pedroCollogno/DTYProject1/PCB/V0/V0 DTY MCAS_etch_silk_bottom.pdf

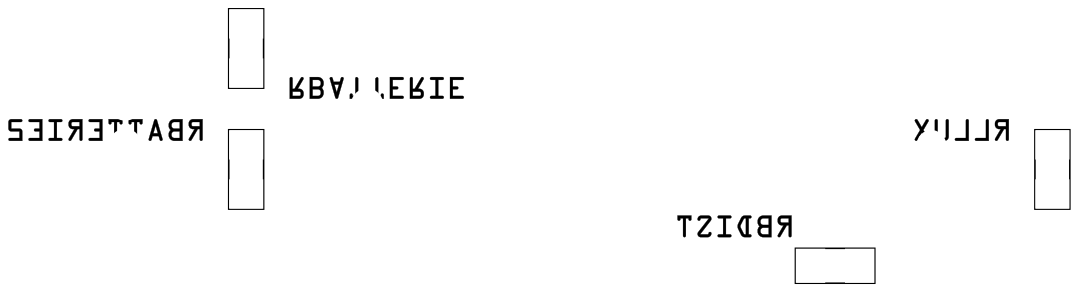
[picture p17: page 1]
