pedroCollogno/DTYProject1/PCB/V0/V0 DTY MCAS_etch_silk_bottom_mirror.pdf

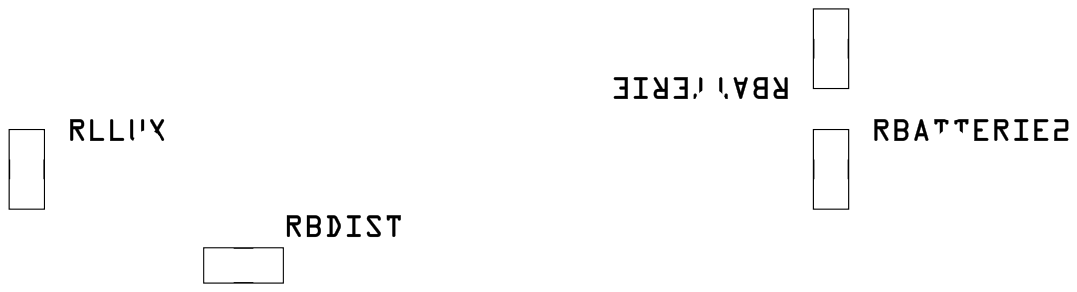
[picture p18: page 1]
