pedroCollogno/DTYProject1/PCB/V0/V0 DTY MCAS_etch_silk_top.pdf

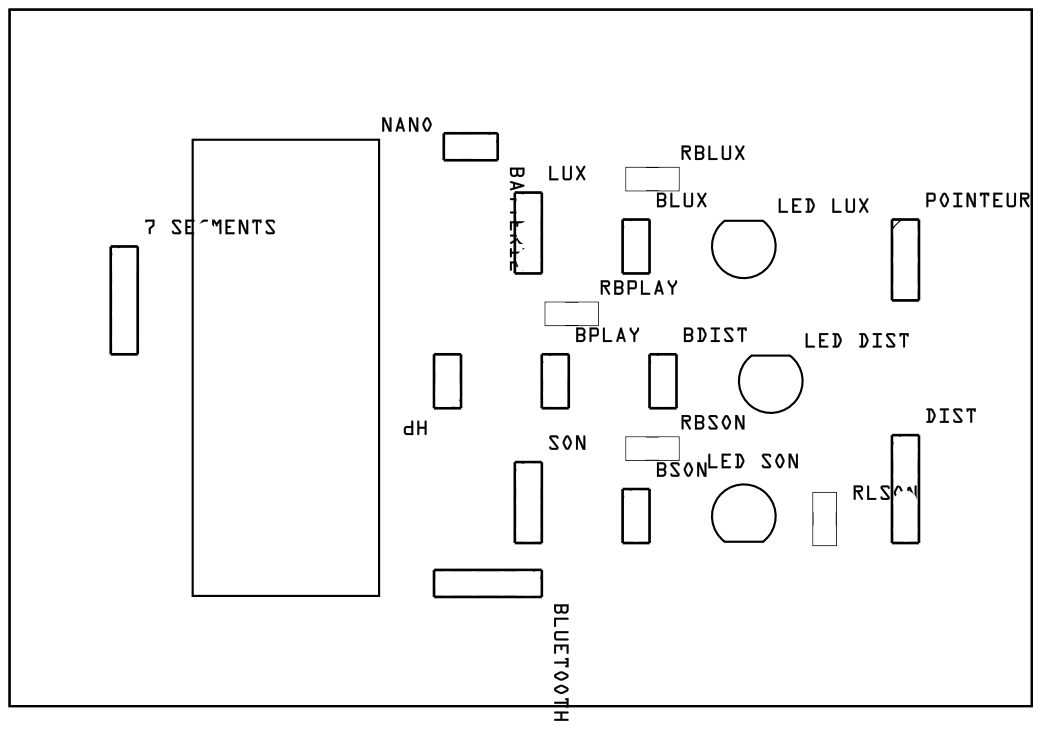
[picture p19: page 1]
