pedroCollogno/DTYProject1/PCB/V0/V0 DTY MCAS_etch_silk_top_mirror.pdf

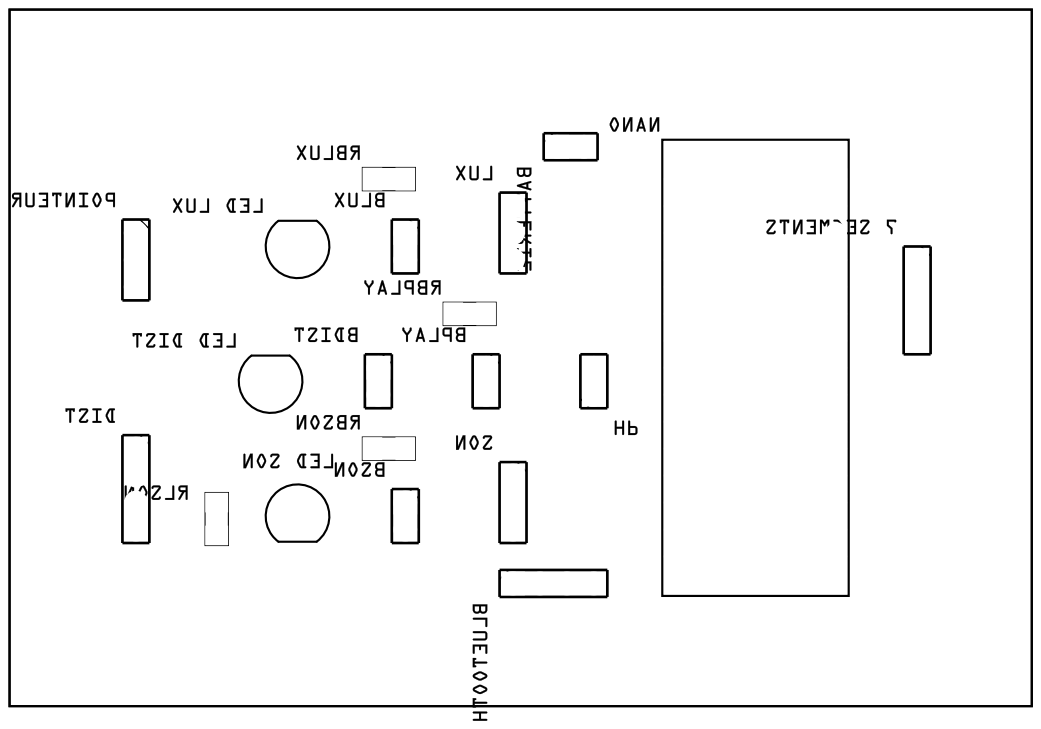
[picture p20: page 1]
